fovezea/EDM-power/main/wifi.c

/*
 * WiFi Integration for EDM Power Project
 * This file shows how to integrate WiFi functionality into your main application
 */

#include "wifi_connect.h"
#include "esp_log.h"
#include "freertos/FreeRTOS.h"
#include "freertos/task.h"

static const char *TAG = "wifi";

// Task that demonstrates WiFi usage
void wifi_task(void *pvParameters)
{
    ESP_LOGI(TAG, "Starting WiFi task");
    
    // Initialize WiFi
    esp_err_t ret = wifi_init_sta();
    if (ret == ESP_OK) {
        ESP_LOGI(TAG, "WiFi connected successfully!");
        
        // Your WiFi-dependent code goes here
        // For example:
        // - Start a web server
        // - Connect to MQTT broker
        // - Send data to cloud service
        // - Receive remote commands
        
        while (1) {
            if (wifi_is_connected()) {
                ESP_LOGI(TAG, "WiFi is connected - EDM system is online");
                
                // Example: Check for remote commands or send status updates
                // This is where you would implement your WiFi-based functionality
                
            } else {
                ESP_LOGW(TAG, "WiFi connection lost, attempting to reconnect...");
                wifi_reconnect();
            }
            
            vTaskDelay(pdMS_TO_TICKS(10000)); // Check every 10 seconds
        }
    } else {
        ESP_LOGE(TAG, "Failed to connect to WiFi");
        
        // Continue without WiFi - your EDM system can still work locally
        while (1) {
            ESP_LOGI(TAG, "EDM system running in offline mode");
            vTaskDelay(pdMS_TO_TICKS(30000)); // Log every 30 seconds
        }
    }
}

// Example of how to add WiFi to your main.c app_main() function:
/*
void app_main(void)
{
    // Your existing initialization code
    pwm_adc_queue = xQueueCreate(1, sizeof(int));
    xTaskCreate(stepper_task, "stepper_task", 4096, NULL, 5, NULL);
    ESP_LOGI(TAG, "Stepper motor example started");

    adc_oneshot_init();
    xTaskCreate(adc_on_capture_task, "adc_on_capture_task", 2048, NULL, 10, NULL);
    xTaskCreate(mcpwm_halfbridge_task, "mcpwm_halfbridge_task", 4096, NULL, 5, NULL);
    
    // Add WiFi functionality
    xTaskCreate(wifi_task, "wifi_task", 4096, NULL, 3, NULL);
    ESP_LOGI(TAG, "WiFi task started");
}
*/ 
